plut0nium/0x42/doc/reset_circuit_v02.asc

C1: cap; 4.7n
C2: cap; 10µ
D1: diode; 1N4148
Q1: npn
R1: res; 2.2k
R2: res; 4.7k
R3: res; 100k
R4: res; 220k
R5: res; 10k
R6: res; 22k
R7: res; 10k
S1: sw; MYSW
S2: sw; MYSW
S3: sw; MYSW
U2: LT1716
V1: signal; 3.3
V2: signal; PULSE(0 3.3 1 0.001 0.001 0.1 5 1)
V3: signal; PULSE(0 3.3 5 0.001 0.001 0.5 5 1)
V4: signal; PULSE(0 3.3 12 0.001 0.001 1 5 1)
Named nets: 0, NRST, IN, BOOT0
.tran 0 20 0
.model MYSW SW(Ron=0.1 Roff=1Meg Vt=.5 Vh=0)
